nradulovic/hw_arguo/ltspice/pamp/pab3bbb-arguo-module.asc

C1: cap; 220n; V=25 Irms=1.76 Rser=0.057522 Lser=3n Rpar=4.4meg Cpar=1p
C2: polcap; 100µ; V=50 Irms=580m Rser=0.16 Lser=0 Rpar=700k Cpar=1p mfg="Nichicon" pn="UPL1H101MPH6" type="Al electrolytic"
C3: polcap; 22µ; V=35 Irms=65m Rser=2.3 Lser=0 Rpar=700k Cpar=1p mfg="Nichicon" pn="UPR1V220MAH" type="Al electrolytic"
C4: cap; 120p; V=100 Irms=20.8m Rser=15.448 Lser=3n Rpar=6.4meg Cpar=1p
C5: cap; 220n; V=25 Irms=1.76 Rser=0.057522 Lser=3n Rpar=4.4meg Cpar=1p
C6: polcap; 1m; V=63 Irms=1.7 Rser=0.042 Lser=0 Rpar=4.4meg Cpar=1p
Cmc1: cap; 120p; V=100 Irms=20.8m Rser=5.448 Lser=3n Rpar=6.4meg Cpar=1p
Cmc2: cap; 120p; V=100 Irms=20.8m Rser=5.448 Lser=3n Rpar=6.4meg Cpar=1p
Cmc: cap; 100p; V=100 Irms=20.8m Rser=5.448 Lser=3n Rpar=6.4meg Cpar=1p
Ctc: cap; 1n2; V=100 Irms=75.3m Rser=2.89088 Lser=3n Rpar=4.4meg Cpar=1p
D1: diode; BAV21
D2: diode; BAV21
D3: diode; BAV21
D5: zener; BZX84B24VL
D6: diode; 1N4148
D7: zener; BZX84B24VL
D8: diode; 1N4148
L1: ind; 15n; Rser=20m
L2: ind; 15n; Rser=20m
L3: ind; 15n; Rser=20m
L4: ind; 20n; Rser=10m
L9: ind; 10n; Rser=10m
L10: ind; 20n; Rser=10m
L12: ind; 10n; Rser=10m
PBIAS1: res; {1+(500*BIAS)}
Q1: pnp; 2SA1381F
Q2: npn; BC546B
Q3: npn; 2SC3503F
Q4: npn; BC546B
Q5: npn; BC546B
Q6: npn; CA_BC550C
Q7: pnp; 2N5401
Q8: npn; CA_BC550C
Q9: pnp; BC556B
Q10: pnp; 2N5401
Q11: pnp; 2N5401
Q12: pnp; 2SA1381F
Q14: npn; 2N5550
Q15: pnp; 2SA1381F
Q16: npn; 2SC3503F
Q17: npn; 2N5550
Q21: npn; MJE340
Qpdh: npn; CA_MJE15032C
Qpdl: pnp; CA_MJE15033C
Qph1: npn; MJL3281A
Qph2: npn; MJL3281A
Qph3: npn; MJL3281A
Qpl1: pnp; MJL1302A
Qpl2: pnp; MJL1302A
Qpl3: pnp; MJL1302A
R1: res; 27
R2: res; 100
R3: res; 100
R4: res; 7k5
R5: res; 2.7
R6: res; 33
R7: res; 750
R8: res; 0.22
R9: res; 150
R10: res; 150
R11: res; 1k
R12: res; 22
R14: res; 0.22
R15: res; 1k
R16: res; 62
R17: res; 470
R18: res; 1k
R19: res; 1k
R20: res; 1k
R21: res; 0.22
R22: res; 62
R23: res; 33
R24: res; 0.22
R25: res; 10k
R26: res; 7k5
R27: res; 10
R28: res; 7k5
R29: res; 7k5
R30: res; 10
R32: res; 2.7
R33: res; 2.7
R34: res; 0.22
R36: res; 0.22
R37: res; 270
R40: res; 2.7
R41: res; 2.7
R45: res; 1k
R47: res; 150
R52: res; 1k5
R53: res; 33
R55: res; 47k
R56: res; 10k
R57: res; 13k
R58: res; 5k6
R60: res; 10k
R61: res; 47k
R63: res; 5k6
R64: res; 13k
R68: res; 2.7
R70: res; 1k
Rrhz: res; 10
Rtc: res; 1k
Named nets: pvcc, pvee, out, ninv, inv, gnd, lgnd, prot
.lib ../spice_root/lib/ONNN_BJT.lib
.lib ../spice_root/lib/STM_D.lib
.lib ../spice_root/lib/FCS_BJT.lib
.lib ../spice_root/lib/FCS_D.lib
.lib ../spice_root/lib/ONNN_D.lib
.lib ../spice_root/lib/TSE_BJT.lib
.lib ../spice_root/lib/TXN_IC.lib
