nradulovic/hw_arguo/ltspice/pamp/pab3bbb-arguo.asc

C1: cap; 470n; Rser=600m Lser=6n Rpar=4.4meg Cpar=1p
C2: polcap; 1m; V=6.3 Irms=1.44 Rser=0.09 Lser=5.5n Rpar=1110k Cpar=3p
C3: polcap; 2m2; V=63 Irms=2.77 Rser=0.070 Lser=5n Rpar=900k Cpar=3p
C4: cap; 470n; Rser=600m Lser=6n Rpar=4.4meg Cpar=1p
C5: polcap; 10m; V=50 Irms=2.5 Rser=0.02 Lser=20n Rpar=40k Cpar=3p
C6: cap; 100n; Rser=700m Lser=7n Rpar=4.4meg Cpar=1p
C7: cap; 100n; Rser=700m Lser=7n Rpar=4.4meg Cpar=1p
C8: cap; 100n; Rser=700m Lser=7n Rpar=4.4meg Cpar=1p
C9: cap; {cf}; Rser=140m Lser=3n Rpar=7.4meg
C10: cap; 100n; Rser=700m Lser=7n Rpar=4.4meg Cpar=1p
C11: cap; 100n
C12: cap; 100n; Rser=700m Lser=7n Rpar=4.4meg Cpar=1p
C13: polcap; 1m; V=6.3 Irms=1.44 Rser=0.09 Lser=5.5n Rpar=1110k Cpar=3p
C14: polcap; 10m; V=50 Irms=2.5 Rser=0.02 Lser=20n Rpar=40k Cpar=3p
C15: cap; 11p; Rser=140m Lser=3n Rpar=7.4meg
C16: cap; 100n; Rser=700m Lser=7n Rpar=4.4meg Cpar=1p
C19: cap; 100n; Rser=700m Lser=7n Rpar=4.4meg Cpar=1p
C20: cap; 100n; Rser=700m Lser=7n Rpar=4.4meg Cpar=1p
C21: cap; 470n; Rser=600m Lser=6n Rpar=4.4meg Cpar=1p
C22: cap; 470n; Rser=600m Lser=6n Rpar=4.4meg Cpar=1p
C23: cap; 470n; Rser=600m Lser=6n Rpar=4.4meg Cpar=1p
C24: cap; 100n; Rser=700m Lser=7n Rpar=4.4meg Cpar=1p
C32: polcap; 2m2; V=63 Irms=2.77 Rser=0.070 Lser=5n Rpar=900k Cpar=3p
Cmc1: cap; 2n2; V=100 Irms=20.8m Rser=5.448 Lser=3n Rpar=6.4meg Cpar=1p
D1: schottky; GBPC3502
D2: schottky; GBPC3502
D3: schottky; GBPC3502
D4: schottky; GBPC3502
D5: diode; 1N4148
D6: diode; 1N4148
D7: schottky; 1N5404
D8: schottky; 1N5404
Ii: current; 0; AC {u(prb)}
L4: ind; 4n; Rser=1m
L19: ind; {Zimg}; Cpar=10p
LPWRGND1: ind2; {con1_len*20n}; Rser={con1_len*.5m}
LPWRGND2: ind2; {con1_len*20n}; Rser={con1_len*.5m}
LSPKN2: ind2; {con2_len*20n}; Rser={con2_len*.5m}
LSPKP: ind2; {con2_len*20n}; Rser={con2_len*.5m}
LTRF: ind2; 4µ; Rser=10m Rpar=3meg Cpar=1p
LVCC: ind2; {con1_len*20n}; Rser={con1_len*.5m}
LVEE: ind2; {con1_len*20n}; Rser={con1_len*.5m}
R1: res; .47
R2: res; {nfb1}
R3: res; {nfb2}
R4: res; 1
R5: res; .47
R6: res; 25m
R7: res; 25m
R8: res; 36k
R12: res; {nfb1}
R13: res; {rf}
R14: res; 100k
R19: res; 2.2
R20: res; {nfb2}
R28: res; 25m
R31: res; 25m
R40: res; 10
R41: res; 15m
R42: res; 10k
R43: res; 15m
R46: res; 10k
R49: res; 10
R54: res; 10
R60: res; {Zreal}
V1: voltage; 0
V2: voltage; SINE(0 {supplyVLTL*sqrt(2)} 50 1m 0 {phi}); Rser={rserl}
V3: voltage; SINE(0 {supplyVLTL*sqrt(2)} 50 1m 0 {phi}); Rser={rserl}
V4: voltage; 0
V5: voltage; SINE(0 {vinput} {freq} 10m 10 0 5)
V6: voltage; 0
V7: voltage; PULSE(0 {vinput} 1u 1n 1n {1/(freq*2)} {1/freq})
V8: voltage; PULSE(0 {-vinput} {1u+(1/(freq*2))} 1n 1n {1/(freq*2)} {1/freq})
V9: voltage; SINE(0 {vinput/2} 19k)
V10: voltage; SINE(0 {vinput/2} 20k 0 0)
V12: voltage; 5
V13: voltage; SINE(0 {vinput} {freq} 310m 10 0 5)
V14: voltage; SINE(0 {vinput} {freq} 0 0 0)
V18: voltage; 0
Vi: voltage; 0; AC {u(-prb)}
X1: pab3bbb-arguo-module
Named nets: x, out, xp, pwrgnd, sgnd, speaker, AC1, AC2, SPK+, SPK-, hvcc, hvee, 0, intermet, impulse, imd, sine, prot
;op
.option plotwinsize=0
.option noopiter
Transient
.four {freq} 10 {iterations} v(SPK+,SPK-)
.param prb=0
.param timestep {1/((262144/8)*freq)}
.param freq=1e3
.param stoptime {iterations/freq}
.ac oct 100 10 100meg
.step param prb list -1 1
AC analysis
.param iterations=120
.param Zimp=8
.param Zreal Zimp/2
.param Zimg (Zimp*sqrt(3))/(4*pi*freq)
.param supplyPWRL=150
.param supplyVLTL=33
.lib ../spice_root/lib/STM_D.lib
.param voutput=28
.param supplyK=0.05
.param rserl={(supplyVLTL*supplyVLTL*supplyK)/supplyPWRL}
.tran 0 {stoptime} 0 {timestep}
.param phi 90
.param con1_len 10
KCON1 LVCC LPWRGND1 LPWRGND2 LVEE 0.8
.param con2_len 10
KCON2 LSPKP LSPKN2 0.8
Konektor zvucnika i zvucnik
Konektor napajanja, star ground i napajanje
Negativna povratna sprega
Circuit parameters
AC sonda
.lib ../spice_root/lib/FCS_D.lib
.param BIAS=0.5
.lib ../spice_root/lib/ONNN_D.lib
.param vinput voutput*(nfb1/nfb2)
.param nfb1=200
.param nfb2=5k1
.param cf=18p
.param rf=1e9
Libraries
.step param Zimp list 10m 100m 1 2 3 4
