nradulovic/hw_arguo/ltspice/pamp/pab3bbb-arguo-module-ds.asc

C1: cap; 220n; V=25 Irms=1.76 Rser=0.057522 Lser=3n Rpar=4.4meg Cpar=1p
C3: polcap; 22µ; V=35 Irms=65m Rser=2.3 Lser=0 Rpar=700k Cpar=1p mfg="Nichicon" pn="UPR1V220MAH" type="Al electrolytic"
Cmc: cap; 100p; V=100 Irms=20.8m Rser=5.448 Lser=3n Rpar=6.4meg Cpar=1p
D1: diode; 1N4148
D2: diode; BAV21
D6: diode; 1N4148
D8: diode; 1N4148
L1: ind; 15n; Rser=20m
L2: ind; 15n; Rser=20m
L3: ind; 15n; Rser=20m
L4: ind; 20n; Rser=10m
L9: ind; 10n; Rser=10m
L10: ind; 20n; Rser=10m
L12: ind; 10n; Rser=10m
PBIAS1: res; {1+(500*BIAS)}
Q1: pnp; 2SA1381F
Q2: npn; 2SC3503F
Q3: npn; 2SC3503F
Q7: pnp; 2N5401
Q11: pnp; 2N5401
Q12: pnp; 2SA1381F
Q21: npn; MJE340
Qpdh: npn; CA_MJE15032C
Qpdl: pnp; CA_MJE15033C
Qph1: npn; MJL3281A
Qph2: npn; MJL3281A
Qph3: npn; MJL3281A
Qph4: npn; MJL3281A
Qpl1: pnp; MJL1302A
Qpl2: pnp; MJL1302A
Qpl3: pnp; MJL1302A
Qpl4: pnp; MJL1302A
R1: res; 1e9
R2: res; 4k7
R3: res; 4k7
R4: res; 7k5
R5: res; 2.7
R6: res; 33
R7: res; 1m
R8: res; 0.22
R9: res; 120
R10: res; 120
R11: res; 1m
R14: res; 0.22
R16: res; 62
R21: res; 0.22
R24: res; 0.22
R27: res; 10
R28: res; 7k5
R29: res; 7k5
R30: res; 10
R32: res; 2.7
R33: res; 2.7
R34: res; 0.22
R36: res; 0.22
R37: res; 270
R40: res; 2.7
R41: res; 2.7
R46: res; 0.22
R47: res; 150
R48: res; 0.22
R51: res; 2.7
R52: res; 1k5
R53: res; 1m
R54: res; 2.7
R64: res; 13k
R68: res; 2.7
Named nets: pvcc, pvee, out, ninv, inv, gnd, lgnd, prot
.lib ../spice_root/lib/ONNN_BJT.lib
.lib ../spice_root/lib/STM_D.lib
.lib ../spice_root/lib/FCS_BJT.lib
.lib ../spice_root/lib/FCS_D.lib
.lib ../spice_root/lib/ONNN_D.lib
.lib ../spice_root/lib/TSE_BJT.lib
.lib ../spice_root/lib/TXN_IC.lib
