nradulovic/hw_arguo/ltspice/pamp/pab3bbb-arguo-sym.asc

C1: cap; 10µ; Rser=700m Lser=7n Rpar=4.4meg Cpar=1p
C2: polcap; 1m; V=6.3 Irms=1.44 Rser=0.09 Lser=5.5n Rpar=1110k Cpar=3p
C3: cap; {cc}; Rser=140m Lser=3n Rpar=7.4meg
C4: polcap; 1m; V=6.3 Irms=1.44 Rser=0.09 Lser=5.5n Rpar=1110k Cpar=3p
C6: polcap; 10m; V=50 Irms=2.5 Rser=0.08 Lser=20n Rpar=40k Cpar=3p
C9: cap; {cf}; Rser=140m Lser=3n Rpar=7.4meg
C10: cap; 100n; Rser=700m Lser=7n Rpar=4.4meg Cpar=1p
C11: cap; 100n
C12: polcap; 470µ; V=6.3 Irms=290m Rser=0.5 Lser=3n Rpar=1100k Cpar=3p
C14: cap; 2n2; Rser=140m Lser=3n Rpar=7.4meg
C16: cap; 100n; Rser=700m Lser=7n Rpar=4.4meg Cpar=1p
C17: polcap; 1000µ; V=63 Irms=2.77 Rser=0.036 Lser=5n Rpar=900k Cpar=3p mfg="Nichicon" pn="UPW1J102MHD6" type="Al electrolytic"
C18: polcap; 220µ; V=50 Irms=1.04 Rser=0.075 Lser=0 Rpar=40k Cpar=3p mfg="Nichicon" pn="UPL1H221MPH" type="Al electrolytic"
C19: polcap; 220µ; V=50 Irms=1.04 Rser=0.075 Lser=0 Rpar=40k Cpar=3p mfg="Nichicon" pn="UPL1H221MPH" type="Al electrolytic"
C21: polcap; 22µ; V=100 Irms=250m Rser=0.71 Lser=2n Rpar=2meg Cpar=2p mfg="Nichicon" pn="UPW1J220MED" type="Al electrolytic"
C22: cap; 470n; Rser=700m Lser=7n Rpar=4.4meg Cpar=1p
C23: cap; 470n; Rser=700m Lser=7n Rpar=4.4meg Cpar=1p
C24: cap; 100n; Rser=700m Lser=7n Rpar=4.4meg Cpar=1p
C25: cap; 100n; Rser=700m Lser=7n Rpar=4.4meg Cpar=1p
C29: cap; 100n; Rser=700m Lser=7n Rpar=4.4meg Cpar=1p
C30: polcap; 10m; V=50 Irms=2.5 Rser=0.08 Lser=20n Rpar=40k Cpar=3p
C31: cap; 100n; Rser=700m Lser=7n Rpar=4.4meg Cpar=1p
C32: polcap; 1000µ; V=63 Irms=2.77 Rser=0.036 Lser=5n Rpar=900k Cpar=3p mfg="Nichicon" pn="UPW1J102MHD6" type="Al electrolytic"
C33: cap; 100n; Rser=700m Lser=7n Rpar=4.4meg Cpar=1p
D1: diode; 1N4148
D2: diode; BAV21
D3: diode; BAV21
D4: diode; BAV21
D5: diode; 1N4148
D6: schottky; GBPC3502
D7: schottky; 1N5404
D8: schottky; 1N5404
D9: schottky; GBPC3502
D10: schottky; GBPC3502
D11: schottky; GBPC3502
D12: diode; 1N4148
D13: diode; 1N4148
D14: diode; 1N4148
D15: diode; 1N4148
Ii: current; 0; AC {u(prb)}
L2: ind; {20n+knfb}
L4: ind; 4n; Rser=1m
L5: ind; 2n; Rser=1m
L6: ind; 2n; Rser=1m
L18: ind; 2n; Rser=1m
L19: ind; {Zimg}; Cpar=10p
LDGND: ind2; {con1_len*20n}; Rser={con1_len*.5m}
LGSPK2: ind2; {con1_len*20n}; Rser={con1_len*.5m}
LPGND: ind2; {con1_len*20n}; Rser={con1_len*.5m}
LPWRGND1: ind2; {con1_len*20n}; Rser={con1_len*.5m}
LPWRGND2: ind2; {con1_len*20n}; Rser={con1_len*.5m}
LSGND: ind2; {con1_len*20n}; Rser={con1_len*.5m}
LSPKN2: ind2; {con2_len*20n}; Rser={con2_len*.5m}
LSPKP: ind2; {con2_len*20n}; Rser={con2_len*.5m}
LTRF: ind2; 2µ; Rser=10m Rpar=3meg Cpar=1p
LVCC: ind2; {con1_len*20n}; Rser={con1_len*.5m}
LVEE: ind2; {con1_len*20n}; Rser={con1_len*.5m}
PBIAS1: res; {1+(500*BIAS)}
Q1: pnp; 2SA1381F
Q2: npn; 2SC3503F
Q4: npn; MJL3281A
Q5: pnp; 2SA1381F
Q6: npn; CA_BC550C
Q7: pnp; CA_BC560C
Q8: npn; CA_BC550C
Q9: pnp; MJL1302A
Q11: pnp; CA_BC560C
Q13: npn; BC847A
Q17: pnp; 2SA1837
Q18: npn; 2SC4793
Q21: npn; MJE340
R1: res; 47
R2: res; {rltpe}
R3: res; {rltpe}
R4: res; {rvase}
R5: res; 2
R6: res; {rvase}
R9: res; {rltpe}
R10: res; {rltpe}
R12: res; {nfb1}
R13: res; {rf}
R14: res; 0.22
R17: res; 22
R18: res; 25m
R19: res; 2.2
R20: res; {nfb2}
R21: res; 0.22
R22: res; 470
R23: res; 470
R24: res; 10k
R25: res; 25m
R26: res; 25m
R27: res; 22
R28: res; 25m
R29: res; 25m
R30: res; 22
R31: res; 25m
R32: res; 50m
R33: res; {nfb1}
R34: res; {nfb2}
R35: res; 5k1
R36: res; 5k1
R37: res; 200
R38: res; 25m
R40: res; 10
R41: res; 15m
R42: res; 10k
R43: res; 15m
R45: res; .47
R46: res; 10k
R47: res; 200
R48: res; 100k
R49: res; 10
R50: res; .47
R52: res; 1k2
R53: res; 11
R54: res; 10
R60: res; {Zreal}
R68: res; 2
V1: voltage; 0
V2: voltage; SINE(0 {supplyVLT*sqrt(2)} 50 1m 0 {phi}); Rser={rser}
V3: voltage; SINE(0 {supplyVLT*sqrt(2)} 50 1m 0 {phi}); Rser={rser}
V4: voltage; 0
V6: voltage; 0
V7: voltage; PULSE(0 {vinput/2} 1u 1n 1n {1/(freq*2)} {1/freq})
V8: voltage; PULSE(0 {-vinput/2} {1u+(1/(freq*2))} 1n 1n {1/(freq*2)} {1/freq})
V9: voltage; SINE(0 {vinput/2} 19k)
V10: voltage; SINE(0 {vinput/2} 20k 0 0)
V11: voltage; SINE(0 {vinput} {freq})
V18: voltage; 0
Vi: voltage; 0; AC {u(-prb)}
Named nets: vcc+, x, vcc-, out, nfb, xp, pwrgnd, sgnd, sinus, pgnd, gspk, speaker, impulse, 0, AC1, AC2, SPK+, SPK-, imd, preout, pin, prot
;op
.option plotwinsize=0
.option noopiter
Transient
.four {freq} 10 10 v(SPK+,SPK-)
.param prb=0
.param timestep {1/((262144/8)*freq)}
.param freq=1e3
.param stoptime {iterations/freq}
.ac oct 100 10 1000meg
.step param prb list -1 1
AC analysis
.param iterations 80
.param Zimp 4
.param Zreal Zimp/2
.param Zimg (Zimp*sqrt(3))/(4*pi*freq)
.param supplyPWR=40
.param supplyVLT=18
.param voutput=16
.param supplyK 0.06
.param rser {(supplyVLT*supplyVLT*supplyK)/(2*supplyPWR)}
.tran 0 {stoptime} 0 {timestep}
.param phi 90
.param con1_len 10
KCON1 LVCC LSGND LGSPK2 LPGND LPWRGND1 LPWRGND2 LVEE LDGND 0.8
.param con2_len 10
KCON2 LSPKP LSPKN2 0.8
Konektor zvucnika i zvucnik
Konektor napajanja, star ground i napajanje
Negativna povratna sprega
Ulazni parametri kola
AC sonda
.param BIAS 0.48
.param knfb 1p
.param vinput voutput*(nfb1/nfb2)
.param nfb1=200
.param nfb2=4k7
.param cf 12p
.param rf 6k8
.param rvase=100
.param rltpc=1k
.param rltpe=100
.param cc=100p
.param rvasc=100
.lib ../spice_root/lib/ONNN_BJT.lib
.lib ../spice_root/lib/STM_D.lib
.lib ../spice_root/lib/FCS_BJT.lib
.lib ../spice_root/lib/FCS_D.lib
.lib ../spice_root/lib/ONNN_D.lib
.lib ../spice_root/lib/TSE_BJT.lib
.lib ../spice_root/lib/TXN_IC.lib
