nradulovic/hw_arguo/ltspice/pamp/pab3bbb-arguo-prot-1slope.asc

D1: diode; BAV21
D2: schottky; BAT46WJ
D3: zener; BZX84B24VL
D4: zener; BZX84B30VL
I1: current; 30m
Q16: npn; 2N3904
Qpdh: npn; 2SC4793
Qph1: npn; MJL3281A
Qph2: npn; MJL3281A
Qph3: npn; MJL3281A
Qph4: npn; MJL3281A
R1: res; 75
R2: res; 2.7
R3: res; 2.7
R4: res; 2.7
R5: res; 2.7
R6: res; 0.1
R7: res; 0.1
R8: res; 0.1
R9: res; 13k
R10: res; 5k6
R11: res; 10k
R12: res; {rs}
R13: res; 1k5
R14: res; 0.1
R15: res; 1k
R16: res; 1k8
R27: res; 10
V1: voltage; PULSE(2 110 2m 108m)
Named nets: pvcc, 0
.lib ../../spice_root/lib/ONNN_BJT.lib
.lib ../../spice_root/lib/STM_D.lib
.lib ../../spice_root/lib/FCS_BJT.lib
.lib ../../spice_root/lib/FCS_D.lib
.lib ../../spice_root/lib/ONNN_D.lib
.lib ../../spice_root/lib/TSE_BJT.lib
.lib ../../spice_root/lib/TXN_IC.lib
.tran 110ms
.param rs=250
