nradulovic/hw_arguo/ltspice/pamp/pab3bbb-arguo-thermal.asc

Qpdh: current; 1.54
Qpdh_Rch: res; 0.1
Qpdh_Rjc: res; 3
Qpdl: current; 1.54
Qpdl_Rch: res; 0.1
Qpdl_Rjc: res; 3
Qph1: current; 22
Qph1_Rch: res; 0.2
Qph1_Rjc: res; 0.625
Qph2: current; 22
Qph2_Rch: res; 0.2
Qph2_Rjc: res; 0.625
Qph3: current; 22
Qph3_Rch: res; 0.2
Qph3_Rjc: res; 0.625
Qpl1: current; 22
Qpl1_Rch: res; 0.2
Qpl1_Rjc: res; 0.625
Qpl2: current; 22
Qpl2_Rch: res; 0.2
Qpl2_Rjc: res; 0.625
Qpl3: current; 22
Qpl3_Rch: res; 0.2
Qpl3_Rjc: res; 0.625
Rh: res; 0.5
Ta: voltage; 45
Named nets: 0, Qpdh_tc, Qpdl_tc, Th, Qpdh_tj, Qpdl_tj, Qph1_tc, Qph1_tj, Ta, Qph2_tc, Qph2_tj, Qph3_tc, Qph3_tj, Qpl1_tc, Qpl1_tj, Qpl2_tc, Qpl2_tj, Qpl3_tc, Qpl3_tj
.op
